Solartraveler/led-toybox/simulation/power-autostart.asc

C1: cap; 0.0000022
C2: cap; 0.00001
M1: nmos; BSS123
R1: res; 330000
R2: res; 330000
R3: res; 0.1
R4: res; 220000
V1: voltage; PULSE(0 3.3 0.1 0.00001 0 0.25 2 4)
Named nets: 0
.tran 1
