Solartraveler/led-toybox/src/apps/common/algorithm/filesystem.c

/*
(c) 2022 by Malte Marwedel

SPDX-License-Identifier: BSD-3-Clause
*/

#include <stdint.h>
#include <stdbool.h>
#include <stdio.h>
#include <string.h>
#include <stdlib.h>

#include "filesystem.h"

#include "ff.h"
#include "json.h"
#include "utility.h"

#include "ledspiellib/flash.h"

FATFS g_fatfs;

uint8_t FilesystemMount(void) {
	if (FlashReady() != true) {
		printf("Error, no valid answer from flash\r\n");
		return 1;
	}
	FRESULT fres;
	fres = f_mount(&g_fatfs, "0", 1);
	if (fres == FR_OK) {
		return 0;
	} else if (fres == FR_NO_FILESYSTEM) {
		printf("Warning, no filesystem\r\n");
		return 2;
	} else {
		printf("Error, mounting returned %u\r\n", (unsigned int)fres);
		return 3;
	}
}

void FilesystemUnmount(void) {
	f_unmount("0");
}

bool FilesystemReadFile(const char * filename, void * data, size_t bufferLen, size_t * pReadLen) {
	bool success = false;
	FIL f;
	if (FR_OK == f_open(&f, filename, FA_READ)) {
		UINT r = 0;
		FRESULT res = f_read(&f, data, bufferLen, &r);
		if (res == FR_OK) {
			success = true;
		} else {
			printf("Warning, could not read >%s<\r\n", filename);
		}
		f_close(&f);
		if (pReadLen) {
			*pReadLen = r;
		}
	}
	return success;
}

bool FilesystemWriteFile(const char * filename, const void * data, size_t dataLen) {
	FIL f;
	bool success = false;
	if (FR_OK == f_open(&f, filename, FA_WRITE | FA_CREATE_ALWAYS)) {
		UINT written = 0;
		FRESULT res = f_write(&f, data, dataLen, &written);
		if ((res == FR_OK) && (written == dataLen)) {
			success = true;
		}
		f_close(&f);
	}
	return success;
}

bool FilesystemWriteEtcFile(const char * filename, const void * data, size_t dataLen) {
	f_mkdir("/etc");
	return FilesystemWriteFile(filename, data, dataLen);
}

bool FilesystemBufferwriterStart(fileBuffer_t * pFileBuffer, const char * filename) {
	if ((pFileBuffer) && (filename)) {
		if (FR_OK == f_open(&(pFileBuffer->f), filename, FA_WRITE | FA_CREATE_ALWAYS)) {
			pFileBuffer->index = 0;
			return true;
		}
	}
	return false;
}

bool FilesystemBufferwriterWb(fileBuffer_t * pFileBuffer) {
	UINT written = 0;
	FRESULT res = f_write(&(pFileBuffer->f), pFileBuffer->buffer, pFileBuffer->index, &written);
	if ((res == FR_OK) && (written == pFileBuffer->index)) {
		pFileBuffer->index = 0;
		return true;
	}
	return false;
}

bool FilesystemBufferwriterAppend(const void * data, size_t len, void * pFileBuffer) {
	size_t i = 0;
	if ((!pFileBuffer) || (!data)) {
		return false;
	}
	fileBuffer_t * pFB = (fileBuffer_t *)pFileBuffer;
	while (i < len) {
		if (pFB->index == FILEBUFFER_SIZE) {
			if (FilesystemBufferwriterWb(pFB) != true) {
				return false;
			}
		}
		size_t todo = len - i;
		size_t left = FILEBUFFER_SIZE - pFB->index;
		size_t add = MIN(todo, left);
		memcpy(pFB->buffer + pFB->index, data + i, add);
		i += add;
		pFB->index += add;
	}
	return true;
}

bool FilesystemBufferwriterClose(fileBuffer_t * pFileBuffer) {
	bool success = false;
	if (pFileBuffer) {
		success = true;
		if (pFileBuffer->index) {
			success &= FilesystemBufferwriterWb(pFileBuffer);
		}
		if (f_close(&(pFileBuffer->f)) != FR_OK) {
			success = false;
		}
	}
	return success;
}

uint32_t FilesystemGetUnusedFilename(const char * directory, const char * prefix) {
	DIR d;
	FILINFO fi;
	uint32_t goodId = 0;
	size_t prefixLen = strlen(prefix);
	if (f_opendir(&d, directory) == FR_OK) {
		while (f_readdir(&d, &fi) == FR_OK) {
			if (!fi.fname[0]) {
				break;
			}
			if (BeginsWith(fi.fname, prefix)) {
				uint32_t num = AsciiScanDec(fi.fname + prefixLen);
				if (num > goodId) {
					goodId = num;
				}
			}
		}
		f_closedir(&d);
		goodId++;
	}
	return goodId;
}
